naifaljohani/DC_Electronic_Load/Hardware/altium_files/electronic_dc_load_v2/electronic_dc_load_v2/3d_lib/TCH-506-8700900.step

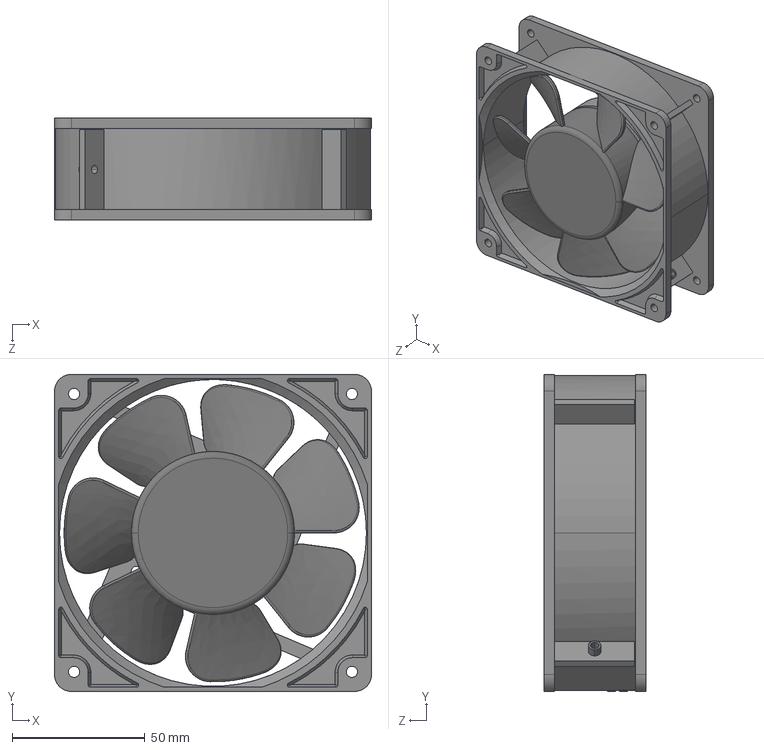
[picture p19: CAD file, 2023-07-22]
Hardware/altium_files/electronic_dc_load_v2/electronic_dc_load_v2/3d_lib/TCH-506-8700900.step
119.5 x 119.6 x 38.5 mm
