naifaljohani/DC_Electronic_Load/Hardware/altium_files/electronic_dc_load_v2/electronic_dc_load_v2/3d_lib/User Library-Fuse-2.STEP

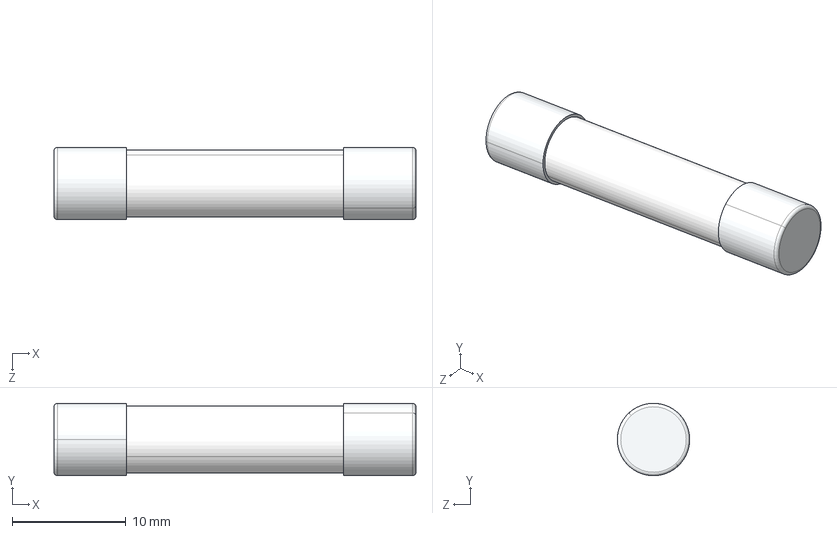
[picture p20: CAD file, 2023-07-22]
Hardware/altium_files/electronic_dc_load_v2/electronic_dc_load_v2/3d_lib/User Library-Fuse-2.STEP
31.8 x 6.35 x 6.35 mm
cap x 2
tube
inners
