naifaljohani/DC_Electronic_Load/Hardware/altium_files/electronic_dc_load_v2/electronic_dc_load_v2/3d_lib/CircuitWorks-DIODE0_7.step

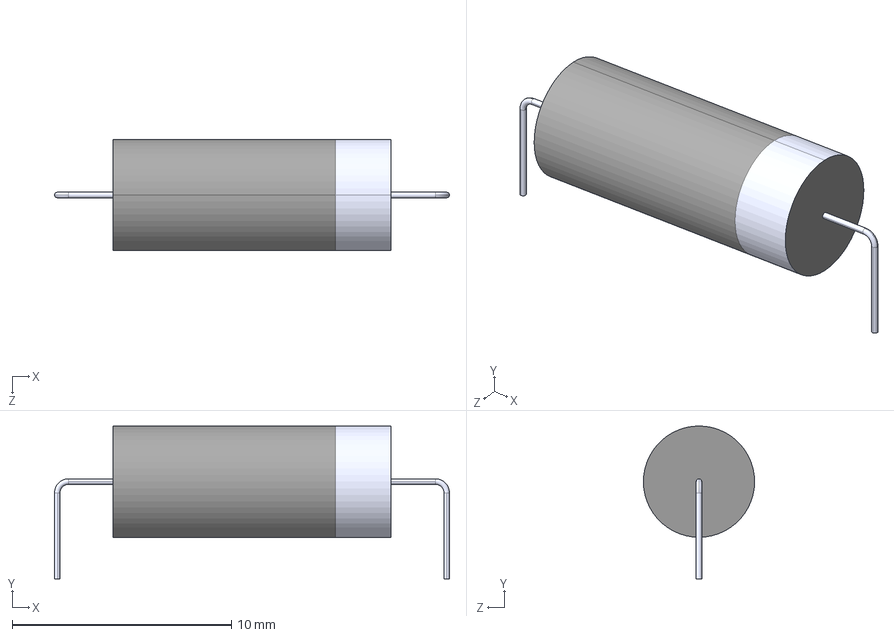
[picture p21: CAD file, 2023-07-22]
Hardware/altium_files/electronic_dc_load_v2/electronic_dc_load_v2/3d_lib/CircuitWorks-DIODE0_7.step
18.0 x 6.99 x 5.08 mm
