naifaljohani/DC_Electronic_Load/Hardware/altium_files/electronic_dc_load_v2/electronic_dc_load_v2/3d_lib/User Library-Sr_ Skived Fin Heat Sink.step

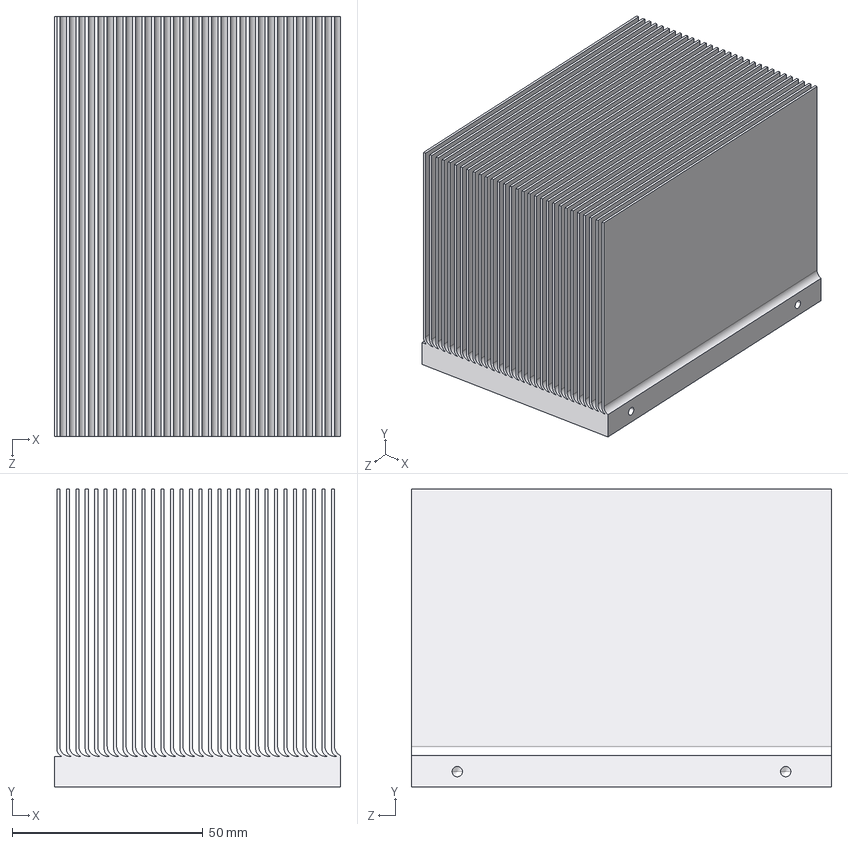
[picture p22: CAD file, 2023-07-22]
Hardware/altium_files/electronic_dc_load_v2/electronic_dc_load_v2/3d_lib/User Library-Sr_ Skived Fin Heat Sink.step
75.0 x 78.0 x 110.0 mm
