naifaljohani/DC_Electronic_Load/Hardware/altium_files/electronic_dc_load_v2/electronic_dc_load_v2/3d_lib/User Library-CE_R200_D200_H460.step

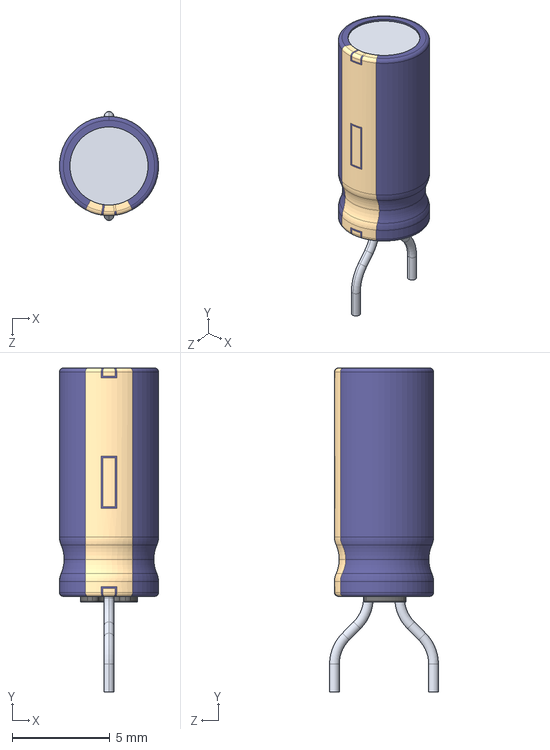
[picture p23: CAD file, 2023-07-22]
Hardware/altium_files/electronic_dc_load_v2/electronic_dc_load_v2/3d_lib/User Library-CE_R200_D200_H460.step
5.08 x 16.6 x 5.58 mm
