naifaljohani/DC_Electronic_Load/Hardware/altium_files/electronic_dc_load_v2/electronic_dc_load_v2/3d_lib/pcb_connector_801-87-005-65-001101.stp

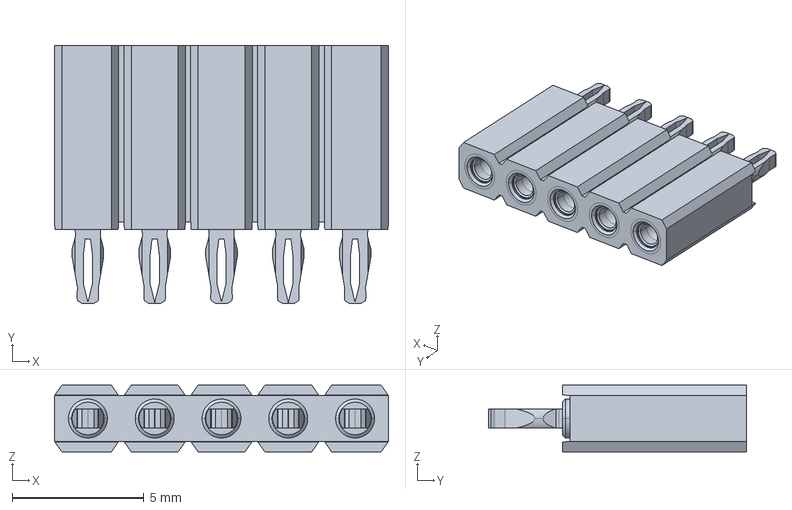
[picture p24: CAD file, 2023-07-22]
Hardware/altium_files/electronic_dc_load_v2/electronic_dc_load_v2/3d_lib/pcb_connector_801-87-005-65-001101.stp
12.7 x 9.80 x 2.54 mm
