naifaljohani/DC_Electronic_Load/Hardware/altium_files/electronic_dc_load_v2/electronic_dc_load_v2/3d_lib/User Library-Fuse_Holder.STEP

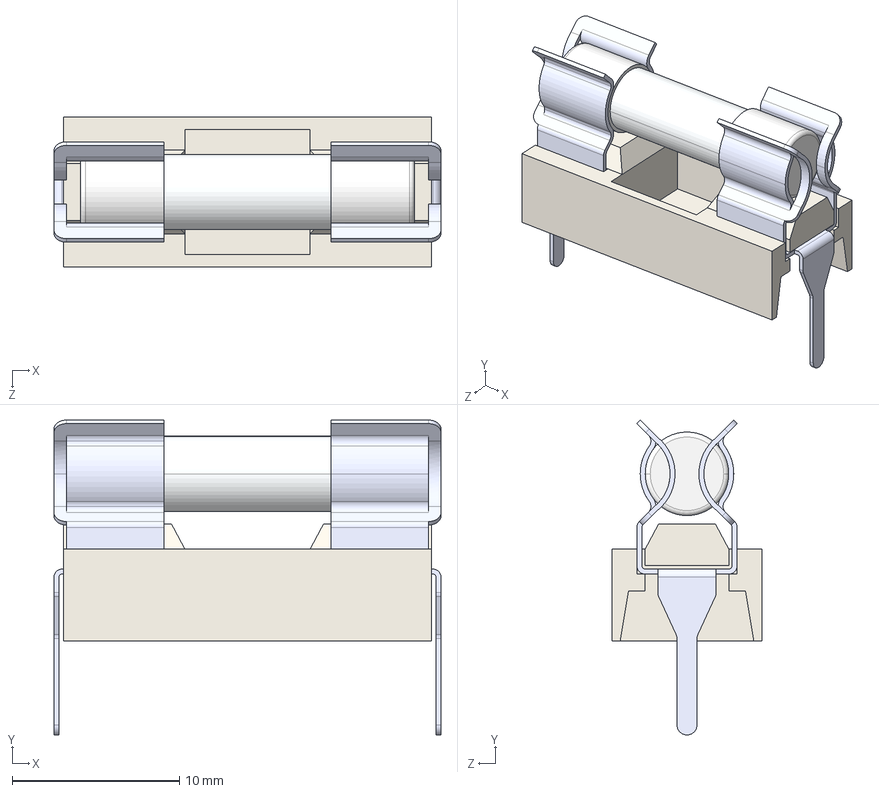
[picture p25: CAD file, 2023-07-22]
Hardware/altium_files/electronic_dc_load_v2/electronic_dc_load_v2/3d_lib/User Library-Fuse_Holder.STEP
23.2 x 18.8 x 9.00 mm
Body_Domyslna
pin_Domyslna x 2
Fuse_Domyslna
