naifaljohani/DC_Electronic_Load/Hardware/altium_files/electronic_dc_load_v2/electronic_dc_load_v2/3d_lib/User Library-BLUE PROJECT BOX OEM.STEP

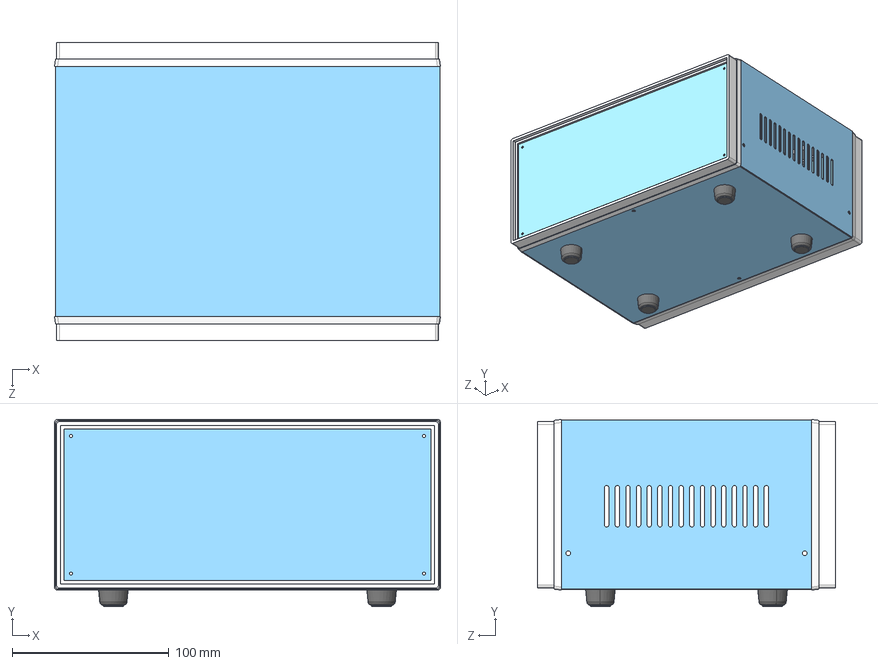
[picture p26: CAD file, 2023-07-22]
Hardware/altium_files/electronic_dc_load_v2/electronic_dc_load_v2/3d_lib/User Library-BLUE PROJECT BOX OEM.STEP
246.6 x 119.6 x 190.1 mm
BOTTOM PLATE
FACE FRAME x 2
FRAME RAIL x 2
FOOT x 4
TOP COVER
11mm_mount stud x 4
FACE PANEL OEM x 2
