naifaljohani/DC_Electronic_Load/Hardware/altium_files/electronic_dc_load_v2/electronic_dc_load_v2/3d_lib/CircuitWorks-DIODE0_41.step

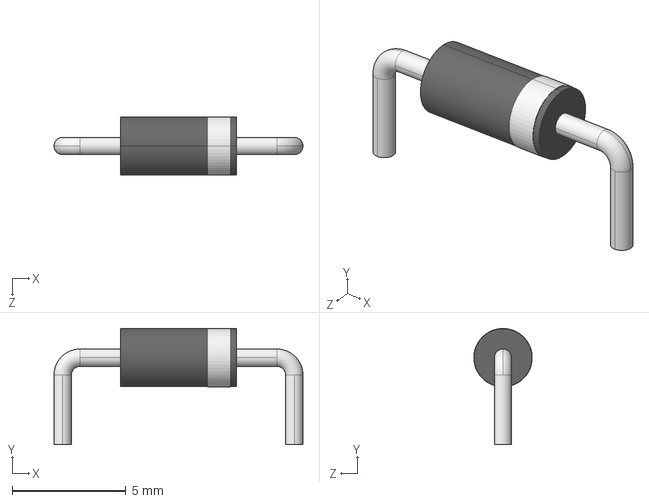
[picture p28: CAD file, 2023-07-22]
Hardware/altium_files/electronic_dc_load_v2/electronic_dc_load_v2/3d_lib/CircuitWorks-DIODE0_41.step
10.9 x 5.09 x 2.57 mm
