naifaljohani/DC_Electronic_Load/Hardware/altium_files/electronic_dc_load_v2/electronic_dc_load_v2/3d_lib/ALSRobot-TO-220-3.STEP

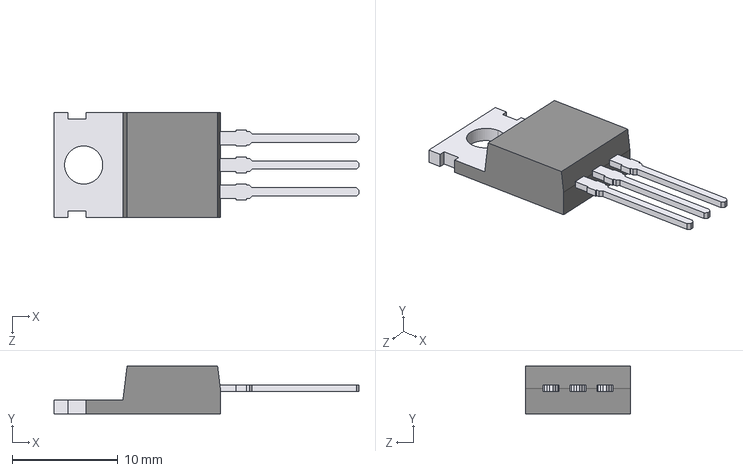
[picture p30: CAD file, 2023-07-22]
Hardware/altium_files/electronic_dc_load_v2/electronic_dc_load_v2/3d_lib/ALSRobot-TO-220-3.STEP
28.8 x 4.50 x 9.90 mm
