naifaljohani/DC_Electronic_Load/Hardware/altium_files/electronic_dc_load_v2/electronic_dc_load_v2/3d_lib/350-80-102-00-006101.stp

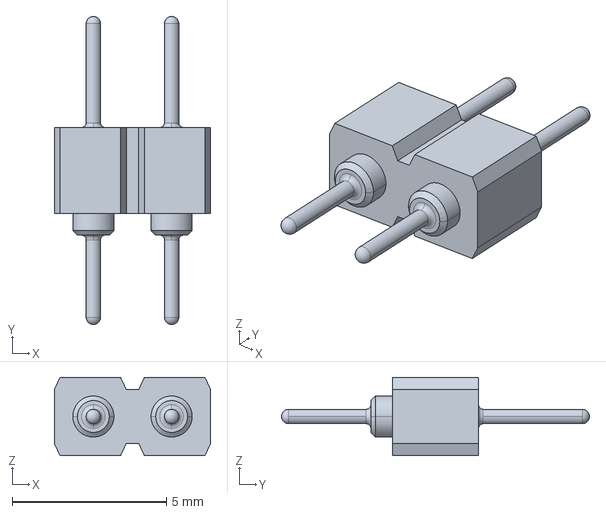
[picture p31: CAD file, 2023-07-22]
Hardware/altium_files/electronic_dc_load_v2/electronic_dc_load_v2/3d_lib/350-80-102-00-006101.stp
5.08 x 10.00 x 2.54 mm
