naifaljohani/DC_Electronic_Load/Hardware/altium_files/electronic_dc_load_v2/electronic_dc_load_v2/3d_lib/pwr220t-35-4r70f.stp

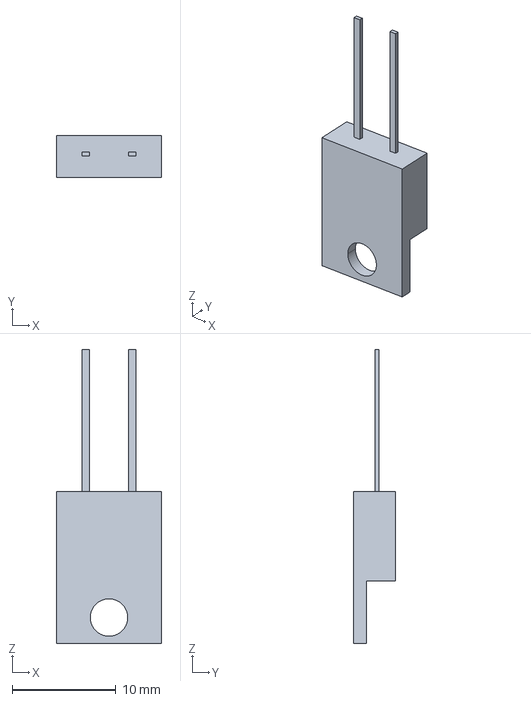
[picture p32: CAD file, 2023-07-22]
Hardware/altium_files/electronic_dc_load_v2/electronic_dc_load_v2/3d_lib/pwr220t-35-4r70f.stp
10.1 x 4.00 x 28.3 mm
