naifaljohani/DC_Electronic_Load/Firmware/source/source.X/dac1_control.h

/* Microchip Technology Inc. and its subsidiaries.  You may use this software 
 * and any derivatives exclusively with Microchip products. 
 * 
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
 * IN NO EVENT WILL MICROCHIP BE LIABLE FOR ANY INDIRECT, SPECIAL, PUNITIVE, 
 * INCIDENTAL OR CONSEQUENTIAL LOSS, DAMAGE, COST OR EXPENSE OF ANY KIND 
 * WHATSOEVER RELATED TO THE SOFTWARE, HOWEVER CAUSED, EVEN IF MICROCHIP HAS 
 * BEEN ADVISED OF THE POSSIBILITY OR THE DAMAGES ARE FORESEEABLE.  TO THE 
 * FULLEST EXTENT ALLOWED BY LAW, MICROCHIP'S TOTAL LIABILITY ON ALL CLAIMS 
 * IN ANY WAY RELATED TO THIS SOFTWARE WILL NOT EXCEED THE AMOUNT OF FEES, IF 
 * ANY, THAT YOU HAVE PAID DIRECTLY TO MICROCHIP FOR THIS SOFTWARE.
 *
 * MICROCHIP PROVIDES THIS SOFTWARE CONDITIONALLY UPON YOUR ACCEPTANCE OF THESE 
 * TERMS. 
 */

/* 
 * File:   
 * Author: 
 * Comments:
 * Revision history: 
 */

// This is a guard condition so that contents of this file are not included
// more than once.  
#ifndef XC_HEADER_TEMPLATE_H
#define	XC_HEADER_TEMPLATE_H

#include <xc.h> // include processor files - each processor file is guarded.  

// TODO Insert appropriate #include <>

// TODO Insert C++ class definitions if appropriate

// TODO Insert declarations

// Comment a function and leverage automatic documentation with slash star star
/**
    <p><b>Function prototype:</b></p>
  
    <p><b>Summary:</b></p>

    <p><b>Description:</b></p>

    <p><b>Precondition:</b></p>

    <p><b>Parameters:</b></p>

    <p><b>Returns:</b></p>

    <p><b>Example:</b></p>
    <code>
 
    </code>

    <p><b>Remarks:</b></p>
 */
// TODO Insert declarations or function prototypes (right here) to leverage 
// live documentation

#ifdef	__cplusplus
extern "C" {
#endif /* __cplusplus */
  
  
  
  

  void dac1_voltage_close_loop(float volt);  
  void dac1_voltage_open_loop(float volt) ;

#ifdef	__cplusplus
}
#endif /* __cplusplus */

#endif	/* XC_HEADER_TEMPLATE_H */
